SanPollo/PerryFi/schematics/perryfi/PerryFi.kicad_sch

## KiCad design schematics/perryfi/PerryFi.kicad_sch (2026-03-06)

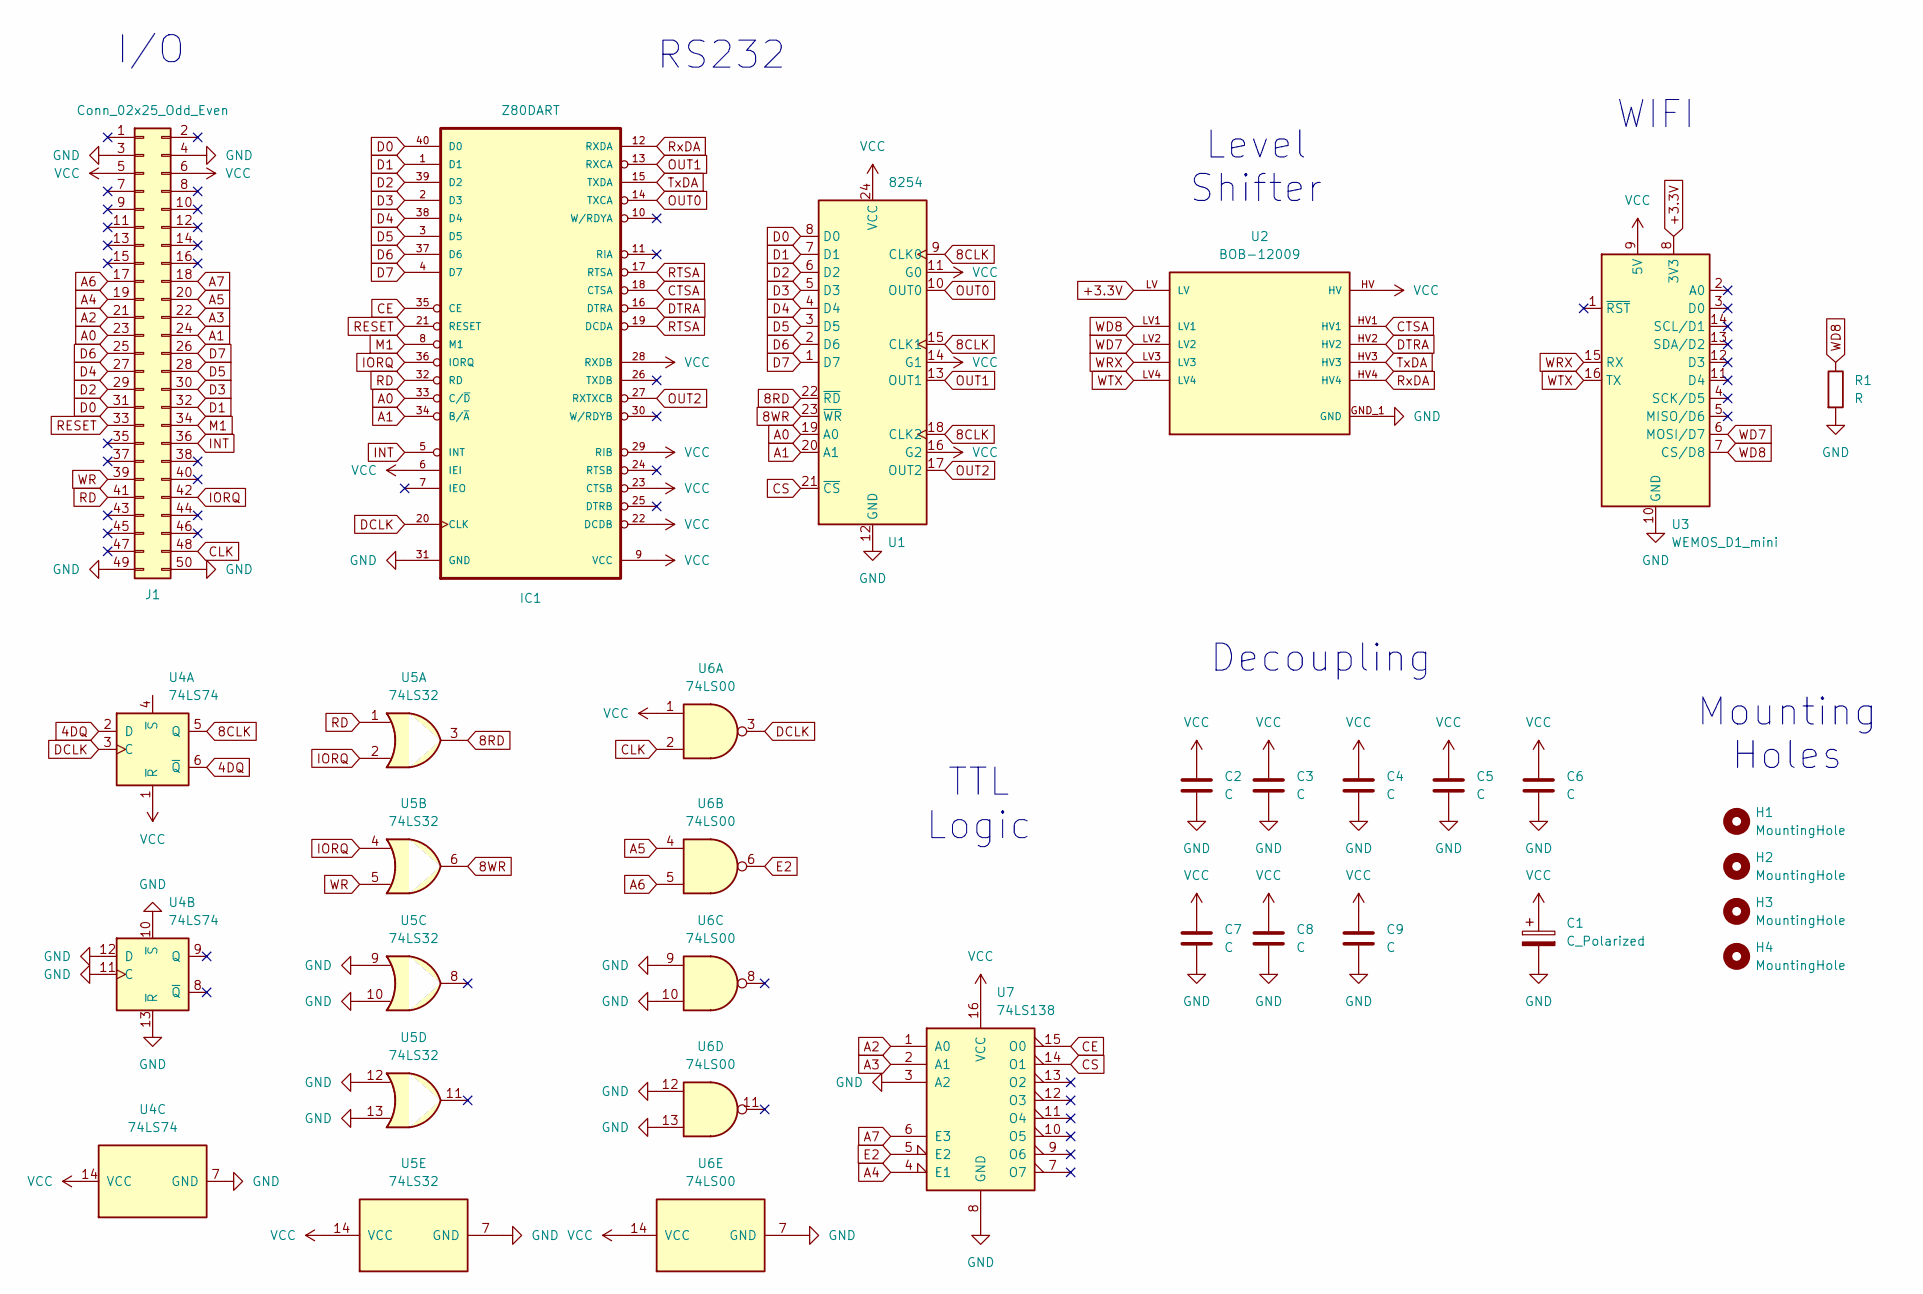
[picture p5: schematic PerryFi.kicad_sch]

Parts:
C1: C_Polarized; CP_Radial_D5.0mm_P2.50mm
C2, C3, C4, C5, C6, C7, C8, C9: C; C_Disc_D3.8mm_W2.6mm_P2.50mm
H1, H2, H3, H4: MountingHole; MountingHole_2.7mm_M2.5_ISO7380
IC1: Z80DART; DIL40
J1: Conn_02x25_Odd_Even; IDC-Header_2x25_P2.54mm_Horizontal
R1: R; R_Axial_DIN0207_L6.3mm_D2.5mm_P7.62mm_Horizontal
U1: 8254; DIP-24_W15.24mm
U2: BOB-12009; CONV_BOB-12009; PARTREV 01
U3: WEMOS_D1_mini; WEMOS_D1_mini_light
U4: 74LS74; DIP-14_W7.62mm
U5: 74LS32; DIP-14_W7.62mm
U6: 74LS00; DIP-14_W7.62mm
U7: 74LS138; DIP-16_W7.62mm

Connections:
4DQ: U4.2 (D), U4.6 (~Q)
8CLK: U1.9 (CLK0), U1.15 (CLK1), U1.18 (CLK2), U4.5 (Q)
8RD: U1.22 (~RD), U5.3
8WR: U1.23 (~WR), U5.6
+3.3V: U2.LV, U3.8 (3V3)
A0: IC1.33 (C/~D), J1.23, U1.19 (A0)
A1: IC1.34 (B/~A), J1.24, U1.20 (A1)
A2: J1.21, U7.1 (A0)
A3: J1.22, U7.2 (A1)
A4: J1.19, U7.4 (E1)
A5: J1.20, U6.4
A6: J1.17, U6.5
A7: J1.18, U7.6 (E3)
CE: IC1.35 (CE), U7.15 (O0)
CLK: J1.48, U6.2
CS: U1.21 (~CS), U7.14 (O1)
CTSA: IC1.18 (CTSA), U2.HV1
D0: IC1.40 (D0), J1.31, U1.8 (D0)
D1: IC1.1 (D1), J1.32, U1.7 (D1)
D2: IC1.39 (D2), J1.29, U1.6 (D2)
D3: IC1.2 (D3), J1.30, U1.5 (D3)
D4: IC1.38 (D4), J1.27, U1.4 (D4)
D5: IC1.3 (D5), J1.28, U1.3 (D5)
D6: IC1.37 (D6), J1.25, U1.2 (D6)
D7: IC1.4 (D7), J1.26, U1.1 (D7)
DCLK: IC1.20 (CLK), U4.3 (C), U6.3
DTRA: IC1.16 (DTRA), U2.HV2
E2: U6.6, U7.5 (E2)
GND: C1.2, C2.2, C3.2, C4.2, C5.2, C6.2, C7.2, C8.2, C9.2, IC1.31 (GND), J1.3, J1.4, J1.49, J1.50, R1.2, U1.12 (GND), U2.GND_1 (GND), U2.GND_2 (GND), U3.10 (GND), U4.7 (GND), U4.10 (~S), U4.11 (C), U4.12 (D), U4.13 (~R), U5.7 (GND), U5.9, U5.10, U5.12, U5.13, U6.7 (GND), U6.9, U6.10, U6.12, U6.13, U7.3 (A2), U7.8 (GND)
INT: IC1.5 (INT), J1.36
IORQ: IC1.36 (IORQ), J1.42, U5.2, U5.4
M1: IC1.8 (M1), J1.34
OUT0: IC1.14 (TXCA), U1.10 (OUT0)
OUT1: IC1.13 (RXCA), U1.13 (OUT1)
OUT2: IC1.27 (RXTXCB), U1.17 (OUT2)
RD: IC1.32 (RD), J1.41, U5.1
RESET: IC1.21 (RESET), J1.33
RTSA: IC1.17 (RTSA), IC1.19 (DCDA)
RxDA: IC1.12 (RXDA), U2.HV4
TxDA: IC1.15 (TXDA), U2.HV3
VCC: C1.1, C2.1, C3.1, C4.1, C5.1, C6.1, C7.1, C8.1, C9.1, IC1.6 (IEI), IC1.9 (VCC), IC1.22 (DCDB), IC1.23 (CTSB), IC1.28 (RXDB), IC1.29 (RIB), J1.5, J1.6, U1.11 (G0), U1.14 (G1), U1.16 (G2), U1.24 (VCC), U2.HV, U3.9 (5V), U4.1 (~R), U4.14 (VCC), U5.14 (VCC), U6.1, U6.14 (VCC), U7.16 (VCC)
WD7: U2.LV2, U3.6 (MOSI/D7)
WD8: R1.1, U2.LV1, U3.7 (CS/D8)
WR: J1.39, U5.5
WRX: U2.LV3, U3.15 (RX)
WTX: U2.LV4, U3.16 (TX)

Notes on the sheet:
Mounting Holes
TTL Logic
WIFI
Decoupling
RS232
Level Shifter
I/O
